Fescron/Ultimate_Adafruit_MacroPad/CIRCUITPY/macros/19_win-clipboard.py

# MACROPAD Hotkeys: Windows "Clipboard"
# BRECHTVE 23/10/2023

app = {                              # REQUIRED dict, must be named 'app'
    'name' : 'Clipboard        1/2', # Application name (<20 chars)
    'macros' : [                     # List of button macros...
        # COLOR    LABEL (<7 chars)    KEY SEQUENCE
        # 1st row ----------
        (0x000000, '',        []),
        (0x000000, '',        []),
        (0x000000, '',        []),
        # 2nd row ----------
        (0x000000, '',        []),
        (0x000000, '',        []),
        (0x000000, '',        []),
        # 3rd row ----------
        (0x000000, '',        []),
        (0x000000, '',        []),
        (0x000000, '',        []),
        # 4th row ----------
        (0x000000, '',        []),
        (0x000000, '',        []),
        (0x000000, '',        []),
        # Encoder button ---
        (0x000000, '',        [])
    ]
}
