Fescron/Ultimate_Adafruit_MacroPad/CIRCUITPY/macros/24_win-altium-schematic-check.py

# MACROPAD Hotkeys: Altium Schematic validation queries for Windows
# BRECHTVE 07/12/2023

from adafruit_macropad import keycodes as Kc # REQUIRED if using Kc.* values

app = {                              # REQUIRED dict, must be named 'app'
    'name' : 'Altium SchmCheck 2/2', # Application name (<20 chars)
    'macros' : [                     # List of button macros...
        # COLOR    LABEL (<7 chars)    KEY SEQUENCE
        # 1st row ----------
        (0x202000, 'cText',  ["(ObjectKind = 'Text String') And ((Color <> '0') Or (Font <> 'Times New Roman, 10, Bold'))"]),
        (0x202000, 'cNote',  ["(ObjectKind = 'Note') And ((TextColor <> '0') Or (FillColor <> '9895935') Or (Font <> 'Times New Roman, 10'))"]),
        (0x202000, 'cNote2', ["(ObjectKind = 'Text Frame') And ((TextColor <> '0') Or (FillColor <> '9895935') Or (Font <> 'Times New Roman, 10') Or (BorderWidth <> 'Smallest'))"]),
        # 2nd row ----------
        (0x202000, 'ctBox',  ["(ObjectKind = 'Text Frame') And ((TextColor <> '0') Or (FillColor <> '14737663') Or (Font <> 'Times New Roman, 16, Bold') Or (Alignment <> 'Center') Or (BorderWidth <> 'Small'))"]),
        (0x202000, 'cDesi',  ["((ObjectKind = 'Parameter') Or (ObjectKind = 'Designator')) And ((Font <> 'Times New Roman, 8') Or (Color <> '8388608'))"]),
        (0x202000, 'cPort',  ["((ObjectKind = 'Parameter') And (ParameterName = 'CrossRef')) And ((Color <> '8388608') Or (Font <> 'Times New Roman, 10'))"]),
        # 3rd row ----------
        (0x000000, '',       []),
        (0x000000, '',       []),
        (0x000000, '',       []),
        # 4th row ----------
        (0x000000, '',       []),
        (0x000000, '',       []),
        (0x000000, '',       []),
        # Encoder button ---
        (0x000000, '',       [Kc.ESCAPE, 0.05, -Kc.ESCAPE, 0.05, Kc.ESCAPE, 0.05, -Kc.ESCAPE, 0.05, Kc.ALT, 0.05, -Kc.ALT, 't', 0.05, 'c'])  # Tools > Cross Probe
    ]
}
